johannes-otto/Librecig/Eichhörnchen/doc/img/20181020_093757.jpg

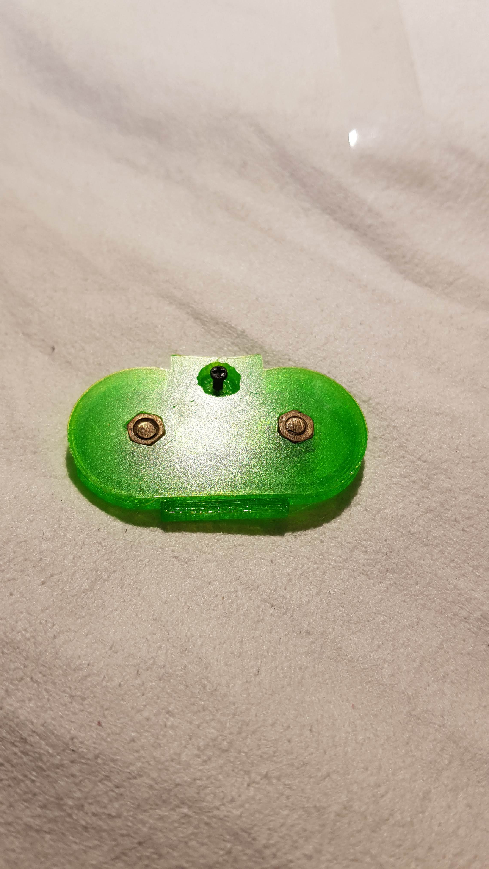
Eichhörnchen/doc/img/20181020_093757.jpg
