johannes-otto/Librecig/Eichhörnchen/doc/img/20181020_103131.jpg

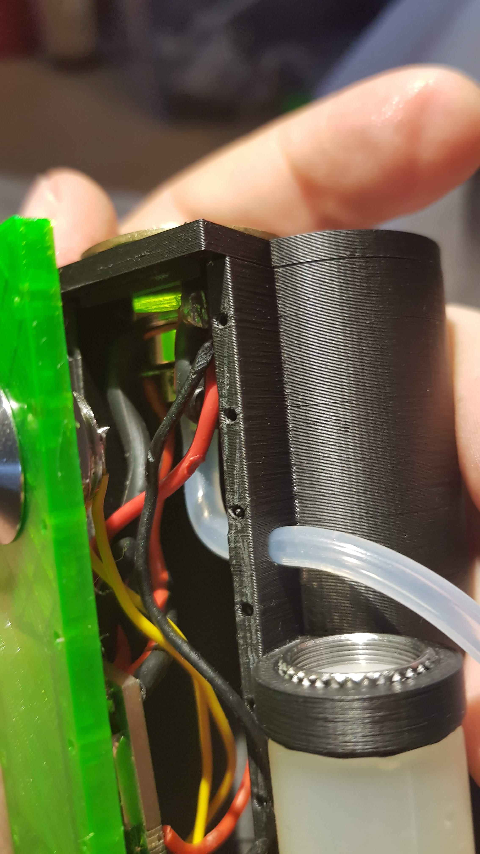
Eichhörnchen/doc/img/20181020_103131.jpg
