johannes-otto/Librecig/Eichhörnchen/doc/img/20181020_105429.jpg

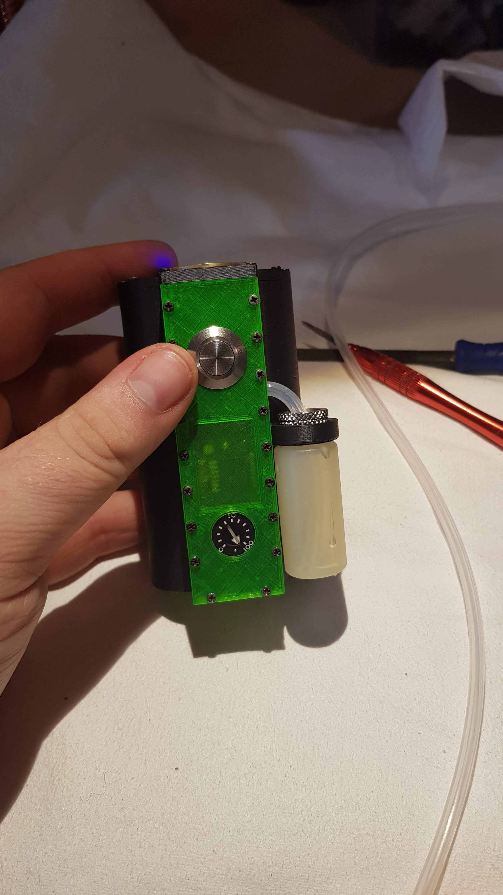
Eichhörnchen/doc/img/20181020_105429.jpg
