johannes-otto/Librecig/Eichhörnchen/doc/img/20181020_105434.jpg

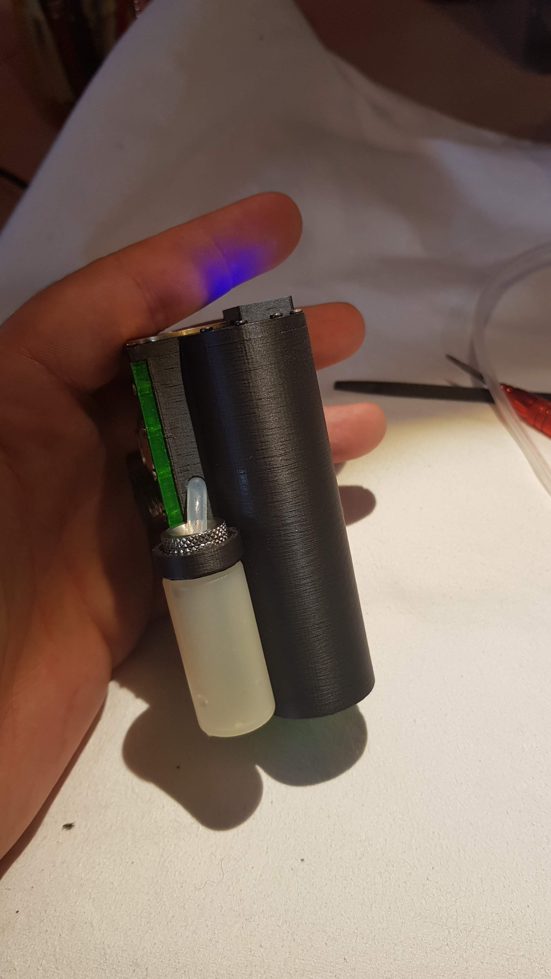
Eichhörnchen/doc/img/20181020_105434.jpg
