johannes-otto/Librecig/Eichhörnchen/doc/img/20181020_105437.jpg

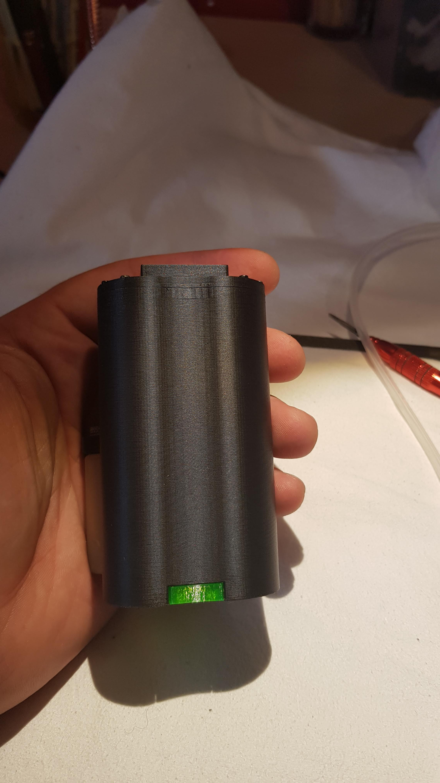
Eichhörnchen/doc/img/20181020_105437.jpg
