johannes-otto/Librecig/Eichhörnchen/doc/img/20181020_105440.jpg

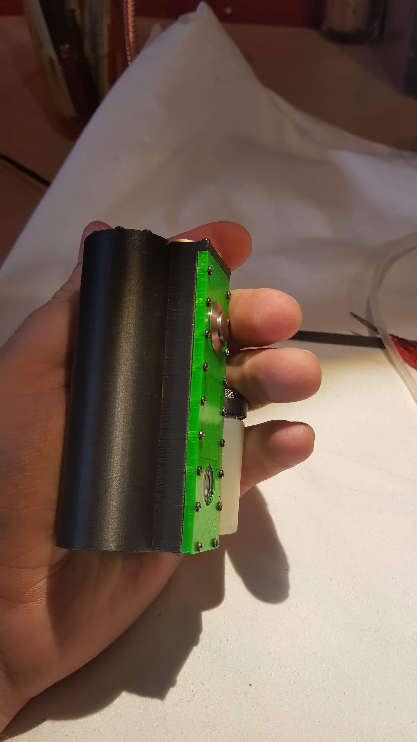
Eichhörnchen/doc/img/20181020_105440.jpg
