johannes-otto/Librecig/Eichhörnchen/doc/img/20181020_105442.jpg

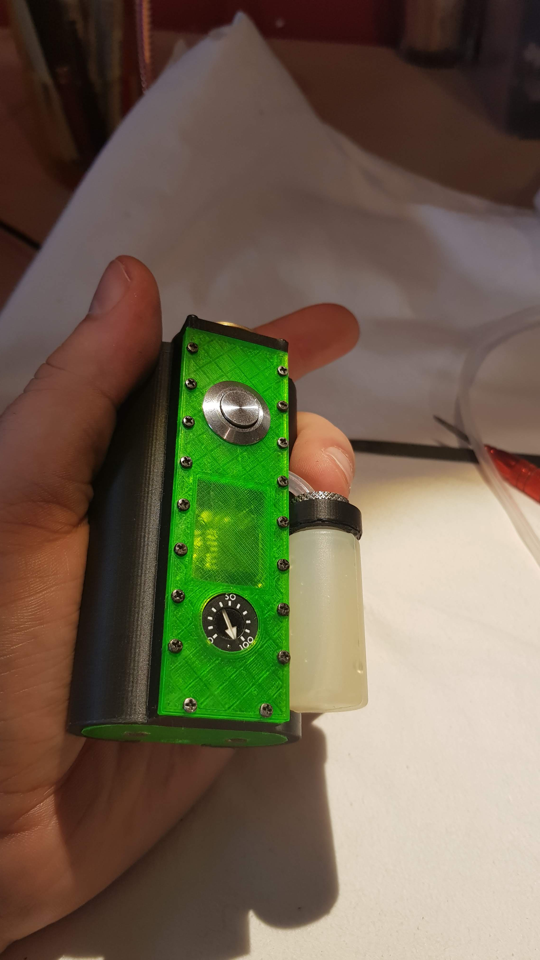
Eichhörnchen/doc/img/20181020_105442.jpg
