johannes-otto/Librecig/Eichhörnchen/doc/img/20181020_105443.jpg

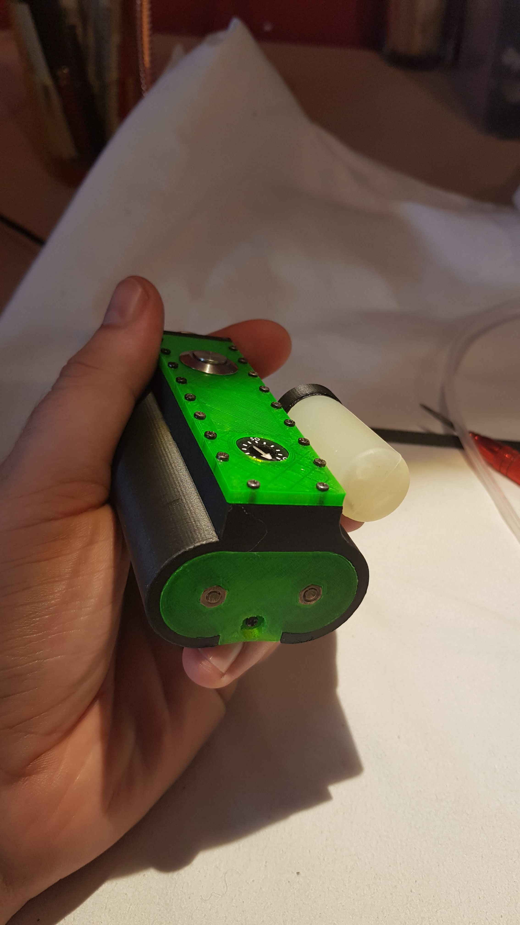
Eichhörnchen/doc/img/20181020_105443.jpg
