johannes-otto/Librecig/Eichhörnchen/doc/img/20181020_105446.jpg

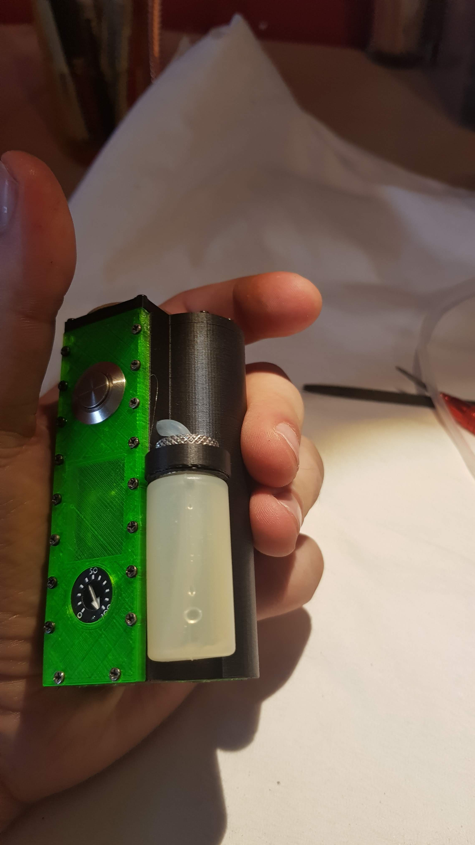
Eichhörnchen/doc/img/20181020_105446.jpg
