johannes-otto/Librecig/Ratte and Variations/doc/images/wire diagrams/ANT PWM Wring Diagram.jpg

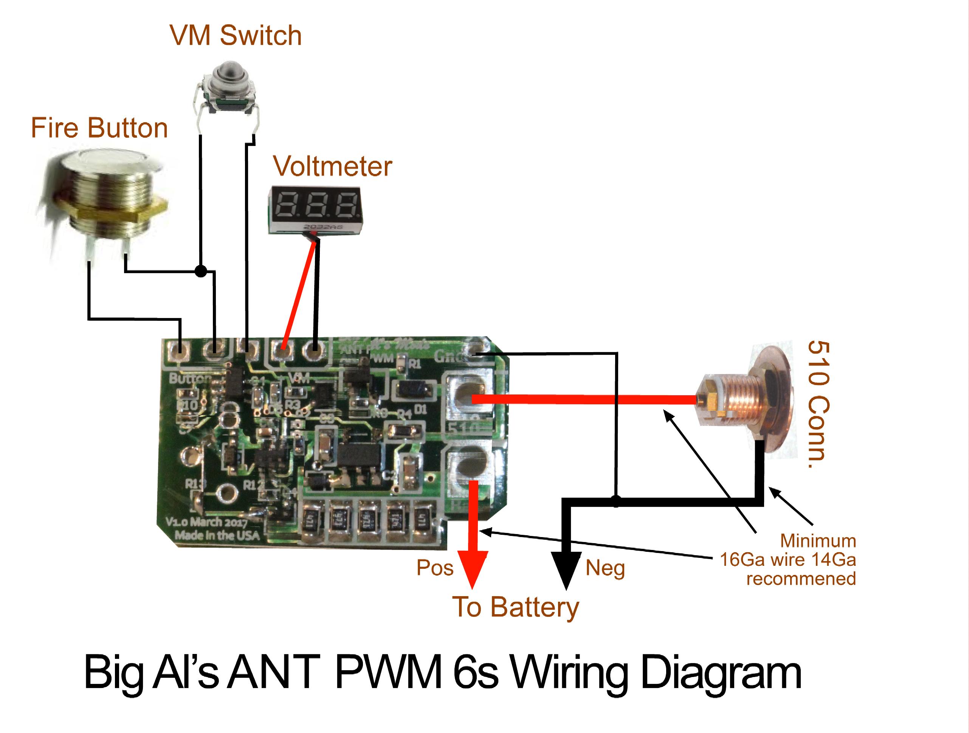
Ratte and Variations/doc/images/wire diagrams/ANT PWM Wring Diagram.jpg
