johannes-otto/Librecig/Großwiesel/Großwiesel v7_Großwiesel v7_body_Großwiesel v7.stl

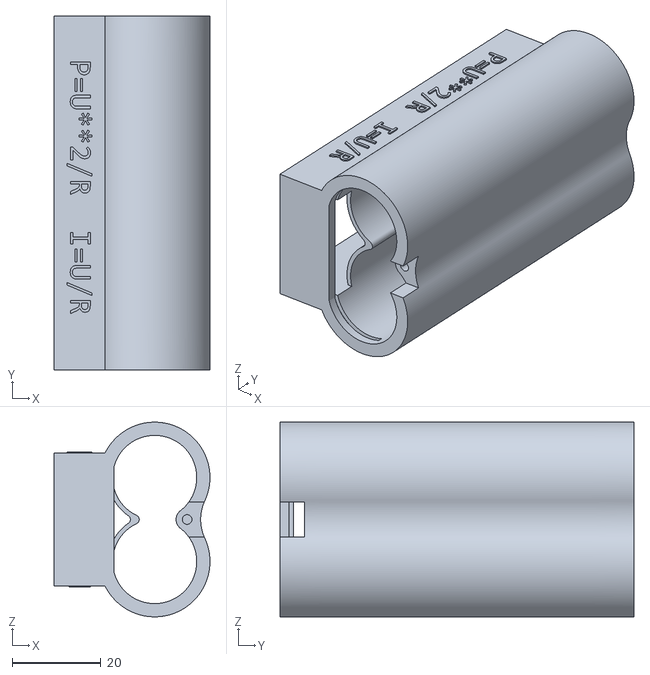
[picture p41: CAD file, 2018-12-22]
Großwiesel/Großwiesel v7_Großwiesel v7_body_Großwiesel v7.stl
35.2 x 80.0 x 44.0
