johannes-otto/Librecig/Großwiesel/v7/Großwiesel v7_Großwiesel v7_top_Großwiesel v7.stl

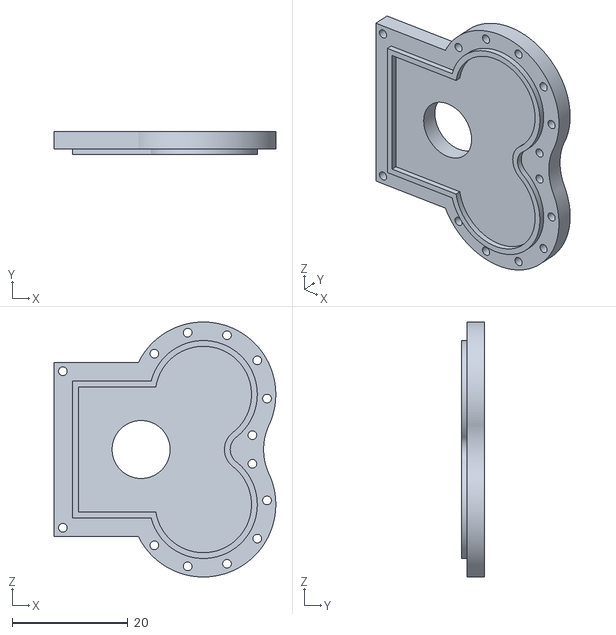
[picture p42: CAD file, 2018-12-22]
Großwiesel/v7/Großwiesel v7_Großwiesel v7_top_Großwiesel v7.stl
38.2 x 4.00 x 44.0
