johannes-otto/Librecig/Ratte and Variations/Leviatan/Leviathan Body.stl

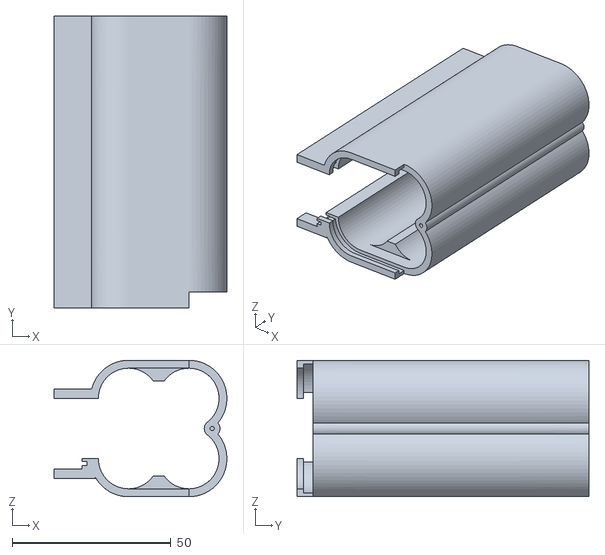
[picture p43: CAD file, 2018-06-19]
Ratte and Variations/Leviatan/Leviathan Body.stl
54.4 x 92.0 x 43.0
