johannes-otto/Librecig/Ratte and Variations/Ratte/Ratte Top.stl

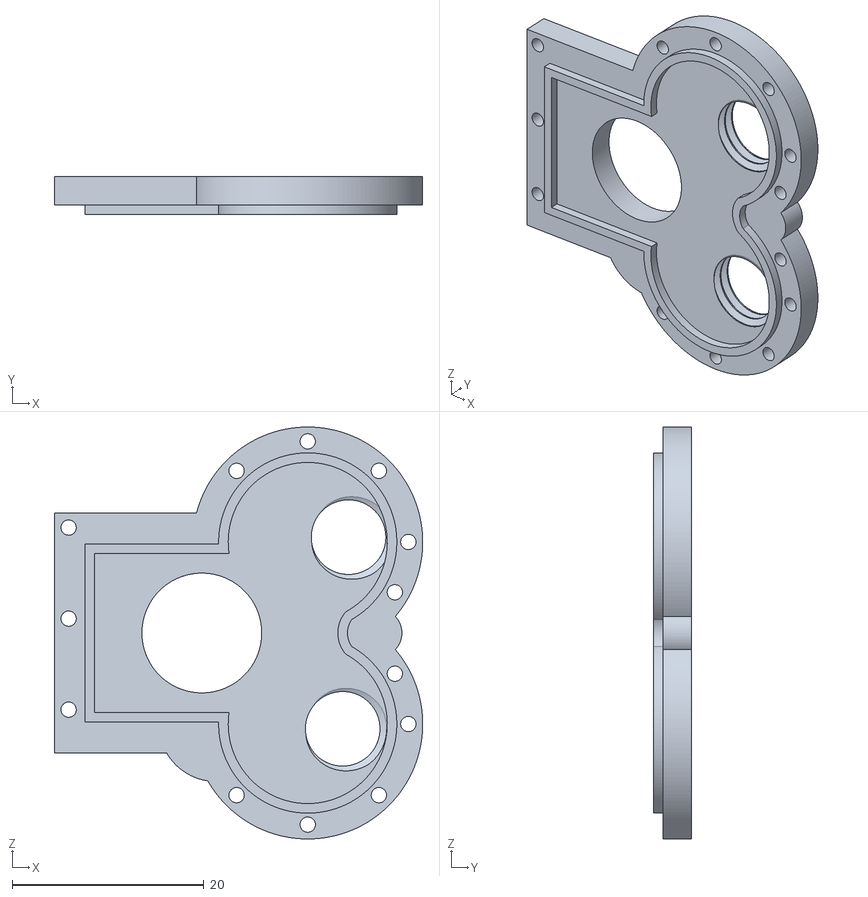
[picture p44: CAD file, 2018-10-05]
Ratte and Variations/Ratte/Ratte Top.stl
38.5 x 4.00 x 43.0
