johannes-otto/Librecig/Ratte and Variations/Wisent/Wisent Battery Door.stl

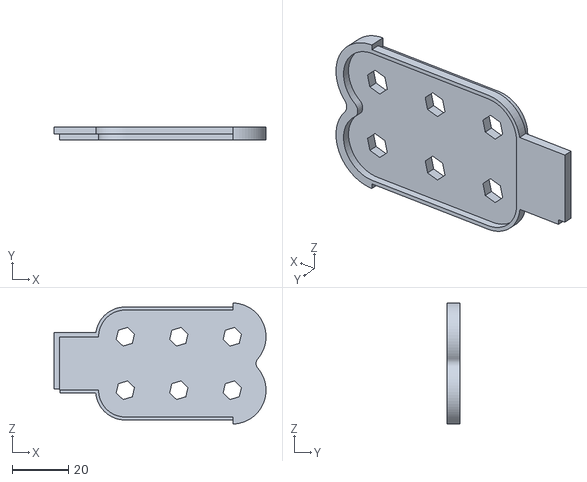
[picture p46: CAD file, 2018-06-10]
Ratte and Variations/Wisent/Wisent Battery Door.stl
75.3 x 4.70 x 43.0
