johannes-otto/Librecig/Wiesel/v4/Wiesel2 v4_Wiesel2 v4_battery door new_Wiesel2 v4.stl

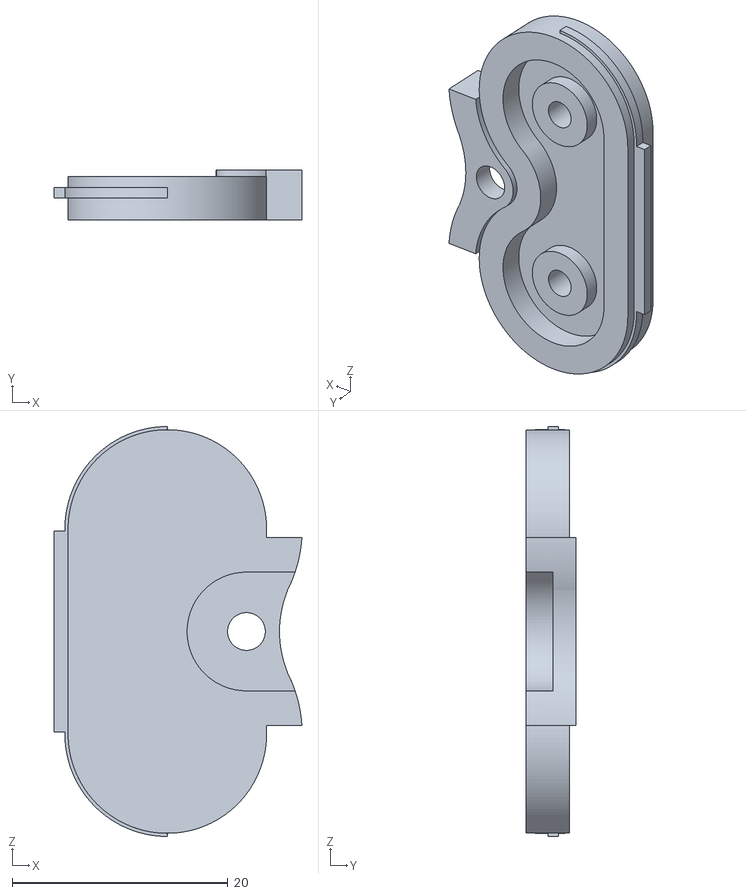
[picture p47: CAD file, 2018-12-22]
Wiesel/v4/Wiesel2 v4_Wiesel2 v4_battery door new_Wiesel2 v4.stl
23.0 x 4.60 x 38.0
