johannes-otto/Librecig/Wiesel/Wiesel 1/v10/spanner.stl

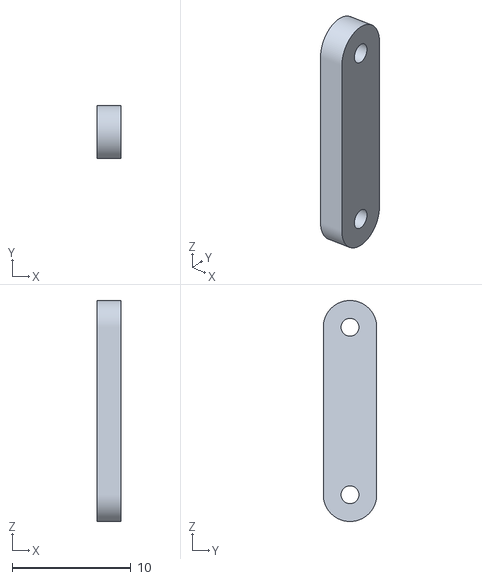
[picture p48: CAD file, 2018-12-09]
Wiesel/Wiesel 1/v10/spanner.stl
2.00 x 4.50 x 18.6
