johannes-otto/Librecig/Battery Compartments/Jonny Drips Subohm Survival Kit/Subohm Survival Kit v4_Subohm Survival Kit v4_Insert_Subohm Survival Kit v4.stl

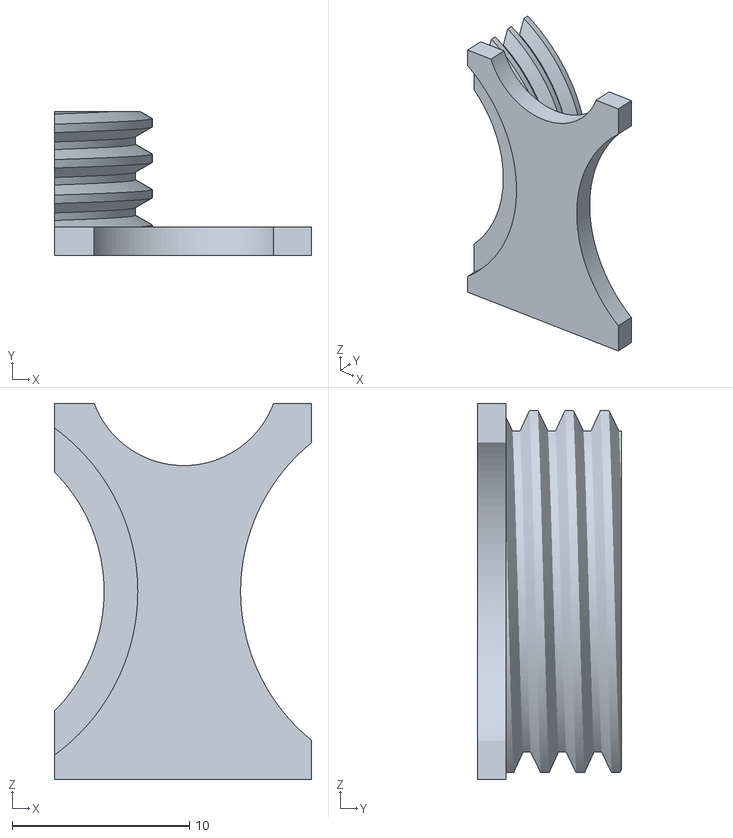
[picture p49: CAD file, 2018-12-22]
Battery Compartments/Jonny Drips Subohm Survival Kit/Subohm Survival Kit v4_Subohm Survival Kit v4_Insert_Subohm Survival Kit v4.stl
14.5 x 8.10 x 21.2
