johannes-otto/Librecig/Eichhörnchen/V1/beautylip.stl

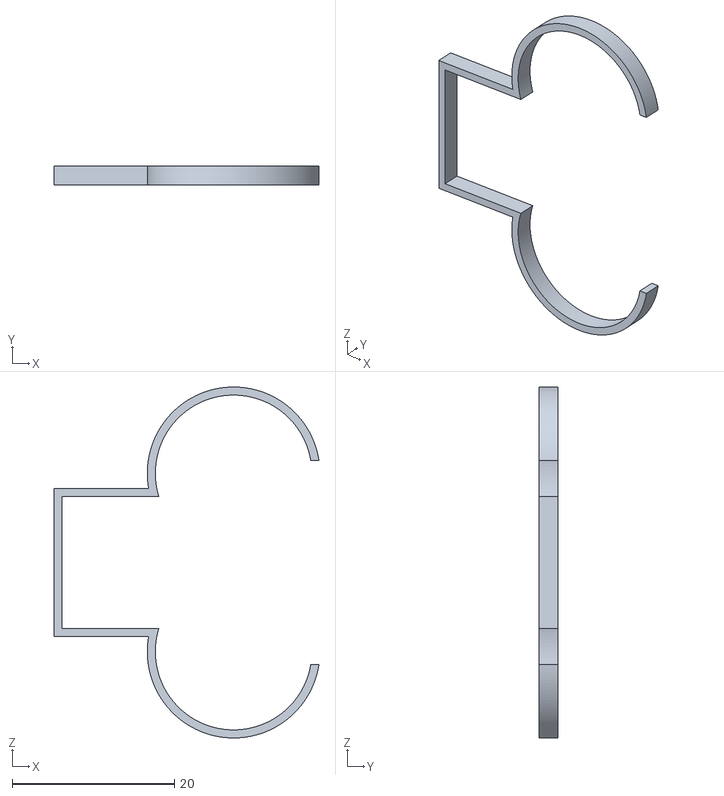
[picture p50: CAD file, 2018-10-05]
Eichhörnchen/V1/beautylip.stl
32.7 x 2.40 x 43.3
