johannes-otto/Librecig/Eichhörnchen/V2 No Squonk/body.stl

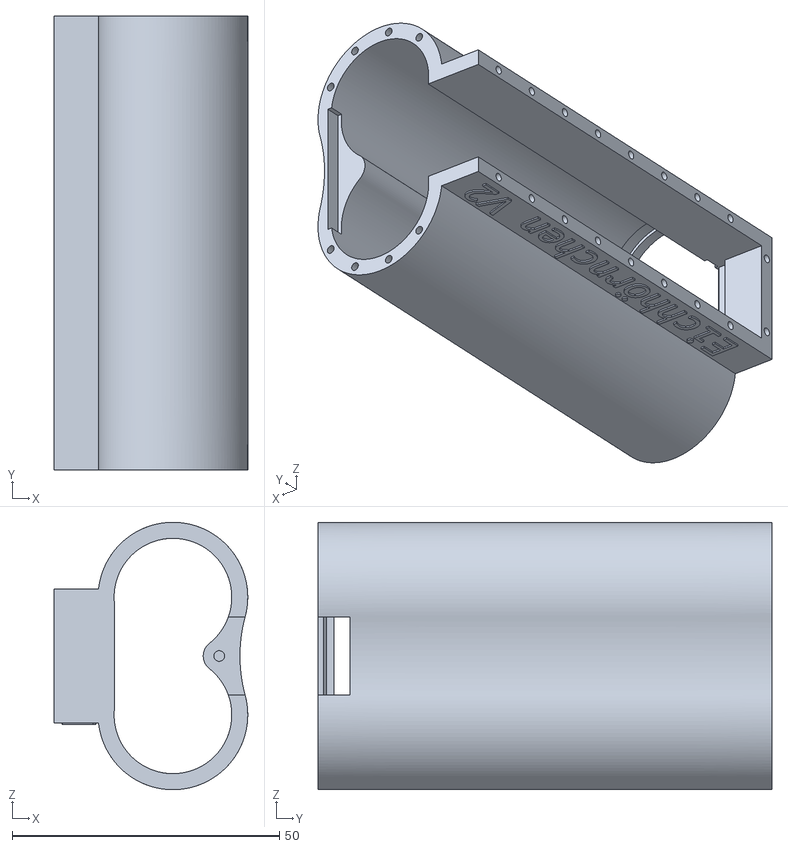
[picture p51: CAD file, 2018-11-24]
Eichhörnchen/V2 No Squonk/body.stl
36.2 x 84.9 x 50.0
