johannes-otto/Librecig/Ratte and Variations/Leviatan/Leviathan Battery Cover.stl

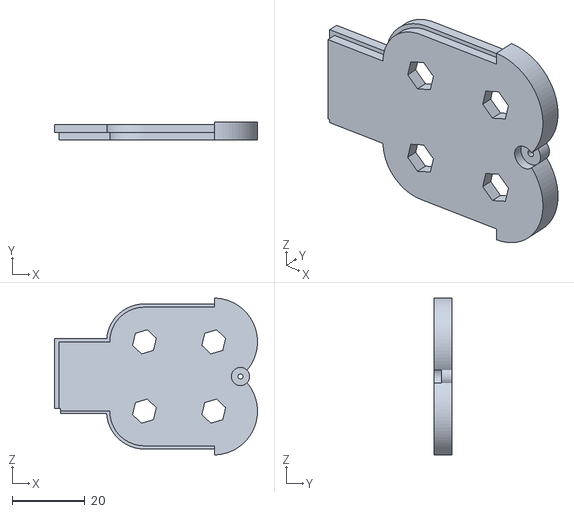
[picture p52: CAD file, 2018-06-19]
Ratte and Variations/Leviatan/Leviathan Battery Cover.stl
55.6 x 4.90 x 43.0
