johannes-otto/Librecig/Ratte and Variations/Ratte/Ratte Body.stl

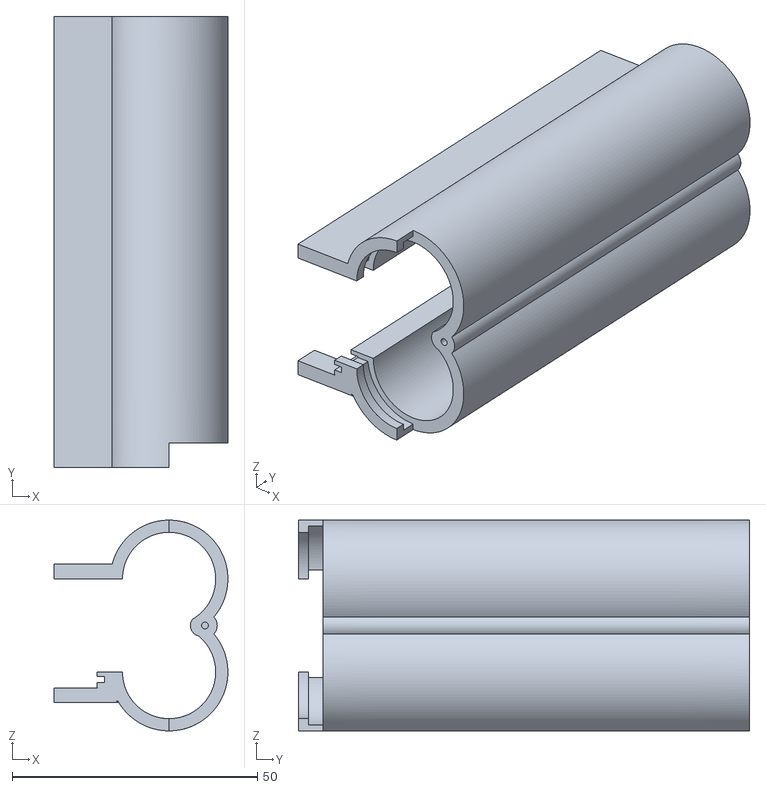
[picture p53: CAD file, 2018-10-05]
Ratte and Variations/Ratte/Ratte Body.stl
35.5 x 92.0 x 43.0
