johannes-otto/Librecig/Ratte and Variations/shared parts/iPWM_Front.stl

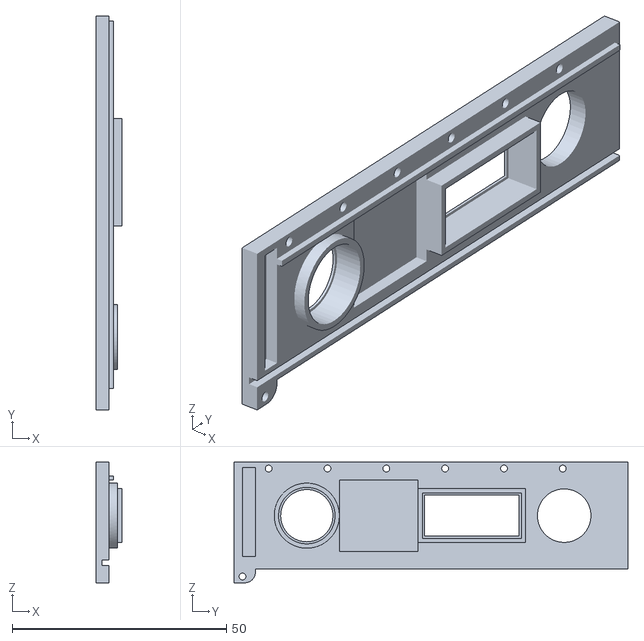
[picture p54: CAD file, 2018-10-05]
Ratte and Variations/shared parts/iPWM_Front.stl
6.00 x 92.0 x 28.2
