johannes-otto/Librecig/Ratte and Variations/Wisent/Wisent Top.stl

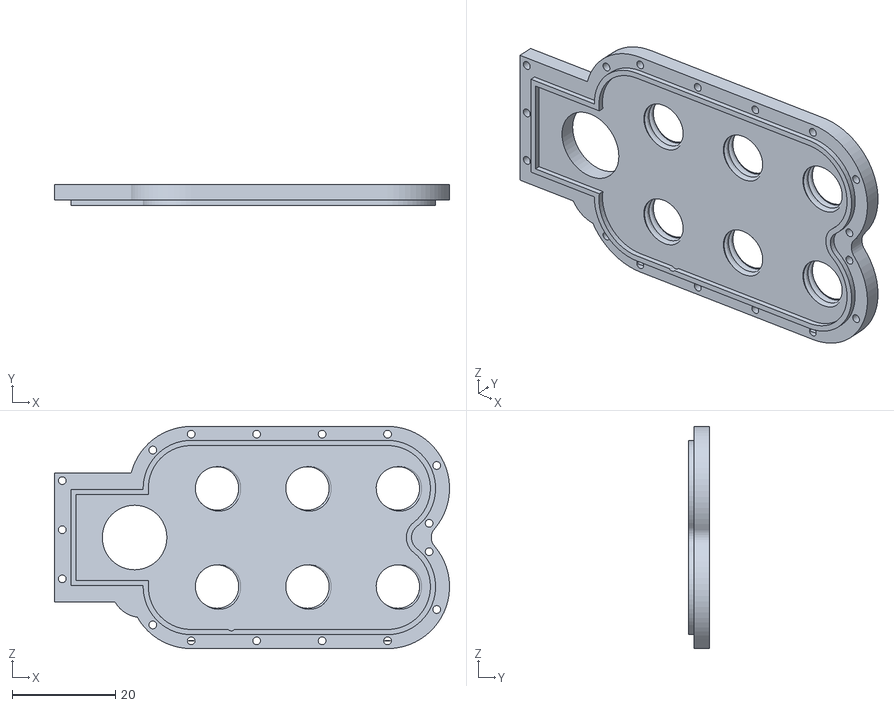
[picture p55: CAD file, 2018-06-10]
Ratte and Variations/Wisent/Wisent Top.stl
76.4 x 4.00 x 43.0
