johannes-otto/Librecig/Wiesel/Wiesel 1/v10/battery door.stl

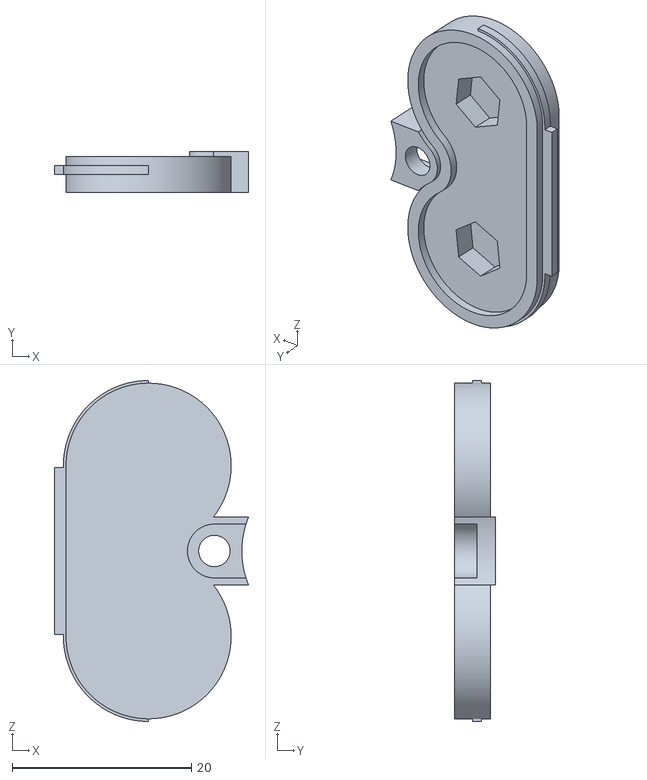
[picture p56: CAD file, 2018-12-09]
Wiesel/Wiesel 1/v10/battery door.stl
21.6 x 4.60 x 38.0
