johannes-otto/Librecig/Eichhörnchen/V2 No Squonk/top.stl

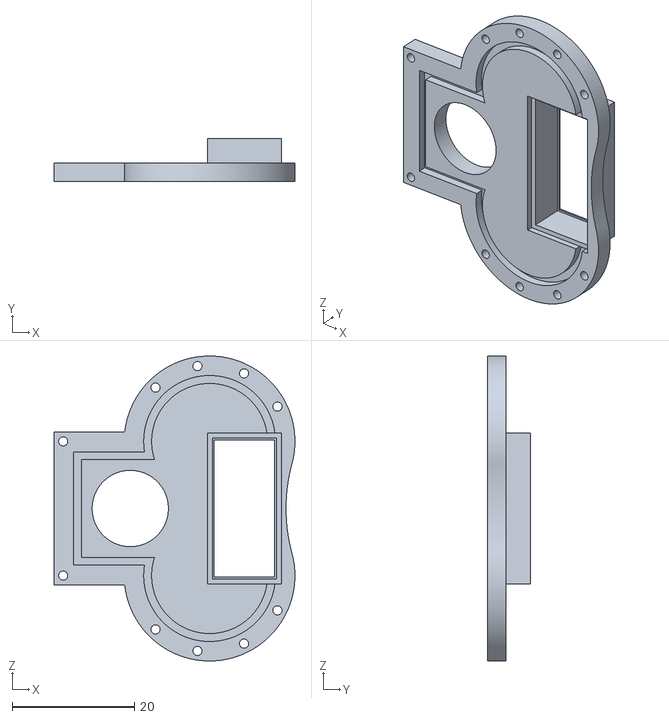
[picture p57: CAD file, 2018-11-24]
Eichhörnchen/V2 No Squonk/top.stl
39.5 x 7.00 x 50.0
