johannes-otto/Librecig/Ratte and Variations/Leviatan/Leviathan Top Pole Spring.stl

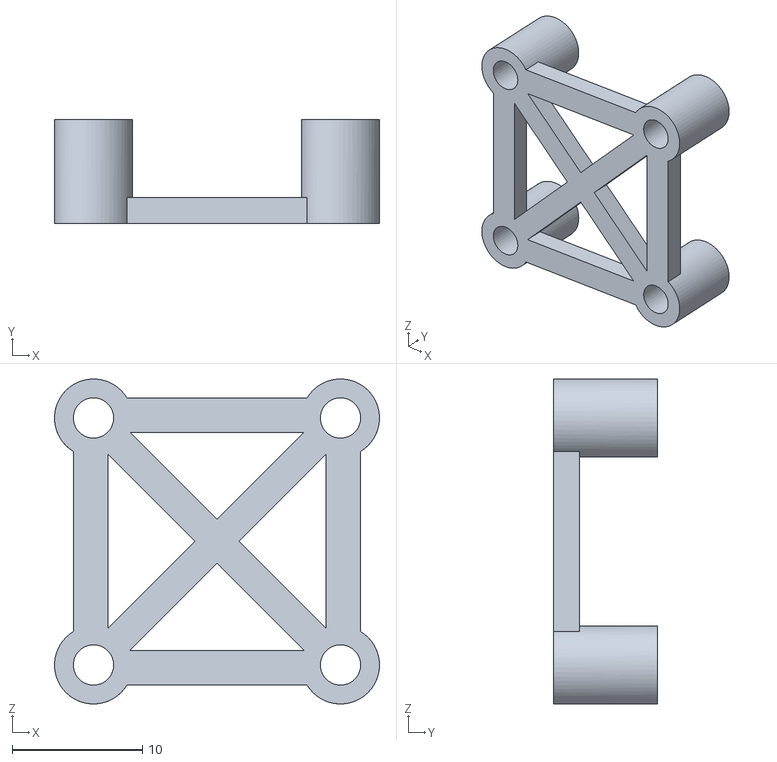
[picture p58: CAD file, 2018-06-19]
Ratte and Variations/Leviatan/Leviathan Top Pole Spring.stl
25.0 x 8.00 x 25.0
