johannes-otto/Librecig/Ratte and Variations/Ratte/Ratte Battery Cover.stl

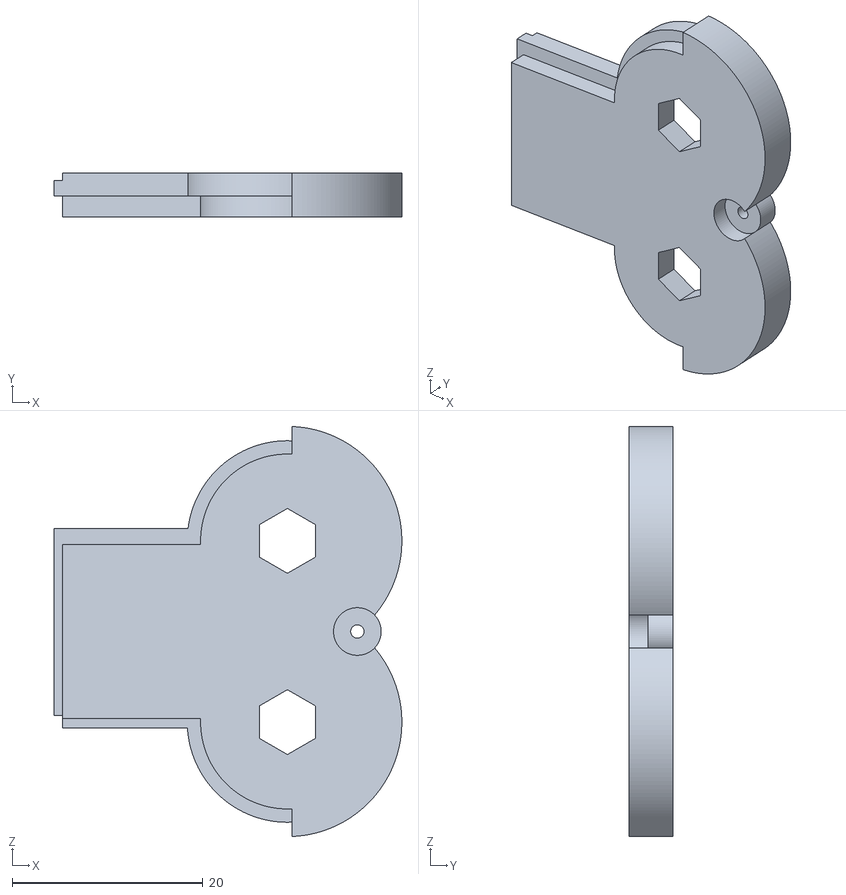
[picture p59: CAD file, 2018-10-05]
Ratte and Variations/Ratte/Ratte Battery Cover.stl
36.5 x 4.60 x 43.0
