johannes-otto/Librecig/Ratte and Variations/shared parts/Mosfet_Front.stl

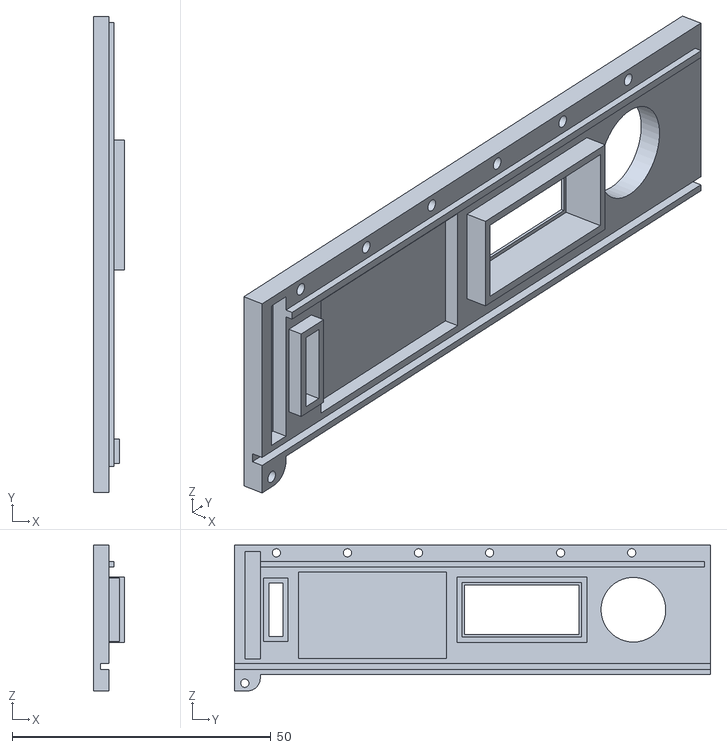
[picture p60: CAD file, 2018-10-05]
Ratte and Variations/shared parts/Mosfet_Front.stl
6.00 x 92.0 x 28.2
