johannes-otto/Librecig/Ratte and Variations/Wisent/Wisent Top Pole Cover 2.stl

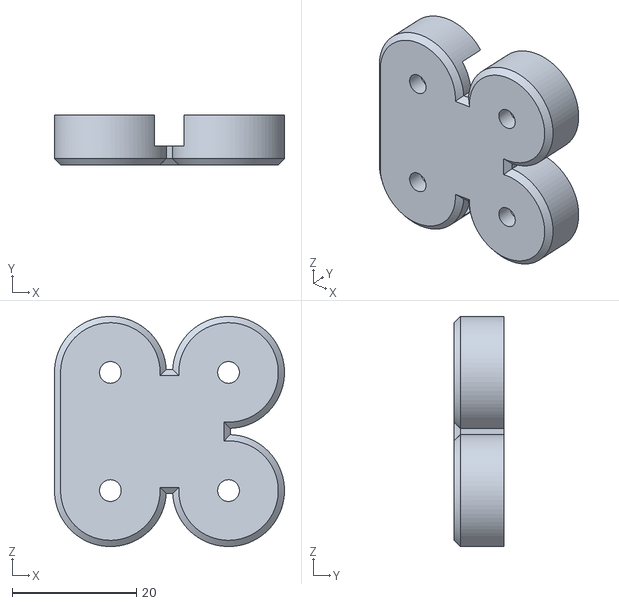
[picture p61: CAD file, 2018-06-03]
Ratte and Variations/Wisent/Wisent Top Pole Cover 2.stl
37.0 x 8.00 x 37.0
