johannes-otto/Librecig/Wiesel/v4/Wiesel2 v4_Wiesel2 v4_terminal_Wiesel2 v4.stl

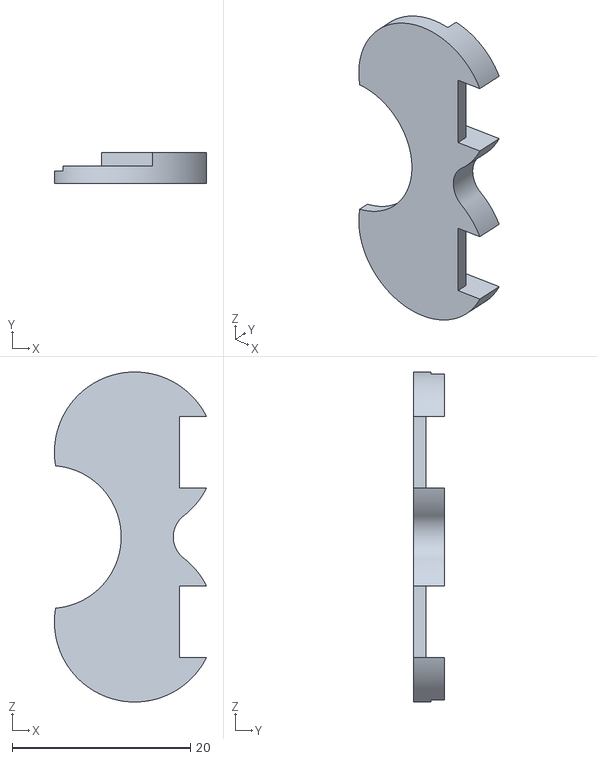
[picture p62: CAD file, 2018-12-22]
Wiesel/v4/Wiesel2 v4_Wiesel2 v4_terminal_Wiesel2 v4.stl
17.1 x 3.50 x 37.0
