johannes-otto/Librecig/Wiesel/Wiesel 1/v10/25mm adapter.stl

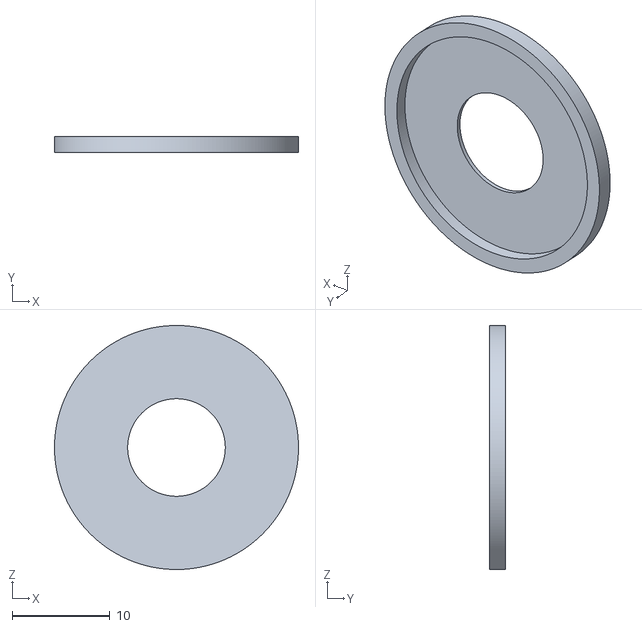
[picture p63: CAD file, 2018-12-09]
Wiesel/Wiesel 1/v10/25mm adapter.stl
25.0 x 1.60 x 25.0
