johannes-otto/Librecig/Eichhörnchen/V2 No Squonk/terminal.stl

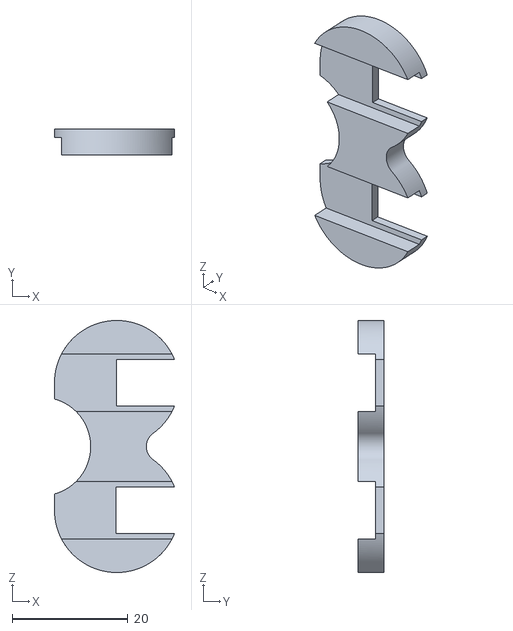
[picture p64: CAD file, 2018-11-24]
Eichhörnchen/V2 No Squonk/terminal.stl
20.7 x 4.50 x 43.5
