johannes-otto/Librecig/Großwiesel/Großwiesel v7_Großwiesel v7_cable clip long_Großwiesel v7.stl

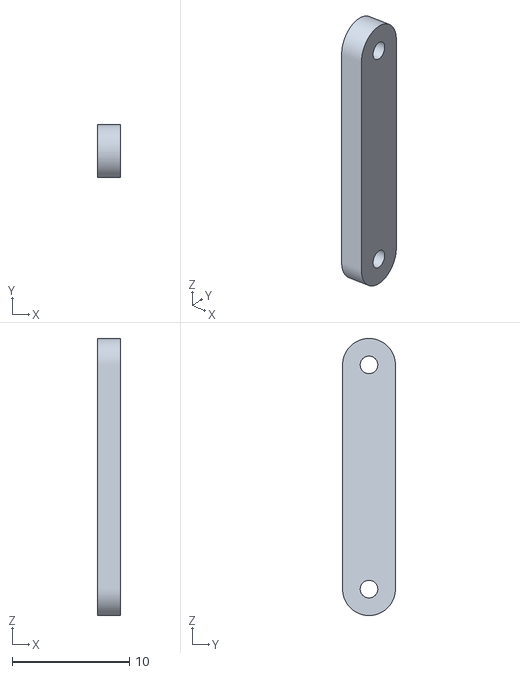
[picture p65: CAD file, 2018-12-22]
Großwiesel/Großwiesel v7_Großwiesel v7_cable clip long_Großwiesel v7.stl
2.00 x 4.50 x 23.6
