johannes-otto/Librecig/Ratte and Variations/Leviatan/Leviathan Top.stl

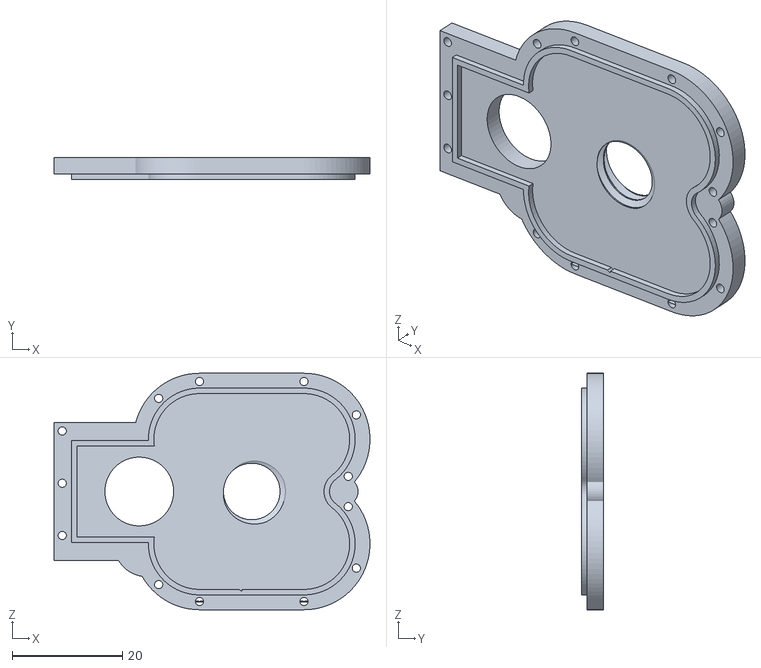
[picture p66: CAD file, 2018-06-19]
Ratte and Variations/Leviatan/Leviathan Top.stl
57.4 x 4.00 x 43.0
