johannes-otto/Librecig/Ratte and Variations/shared parts/New Squonk Side Panel 2.stl

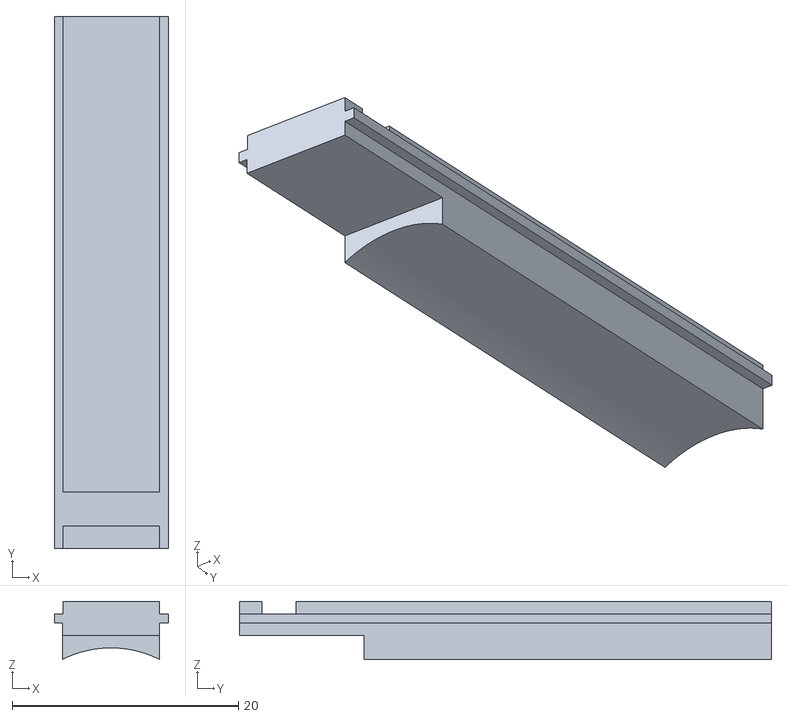
[picture p67: CAD file, 2018-10-05]
Ratte and Variations/shared parts/New Squonk Side Panel 2.stl
10.1 x 47.0 x 5.13
