johannes-otto/Librecig/Ratte and Variations/Wisent/Wisent Top Pole Cover 1.stl

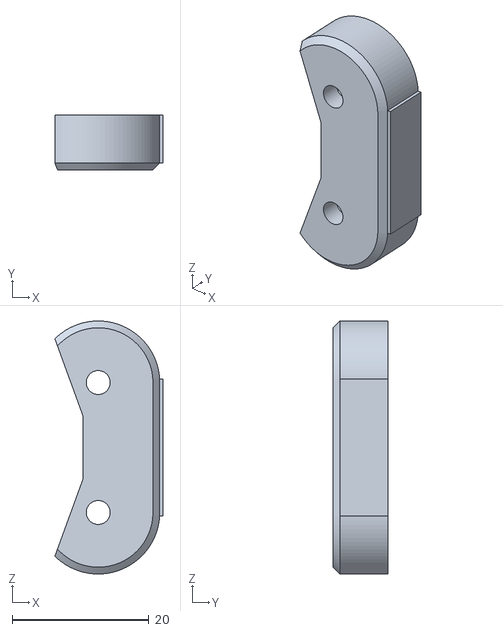
[picture p68: CAD file, 2018-06-02]
Ratte and Variations/Wisent/Wisent Top Pole Cover 1.stl
15.8 x 8.00 x 37.0
