johannes-otto/Librecig/Wiesel/Wiesel 1/v10/terminal.stl

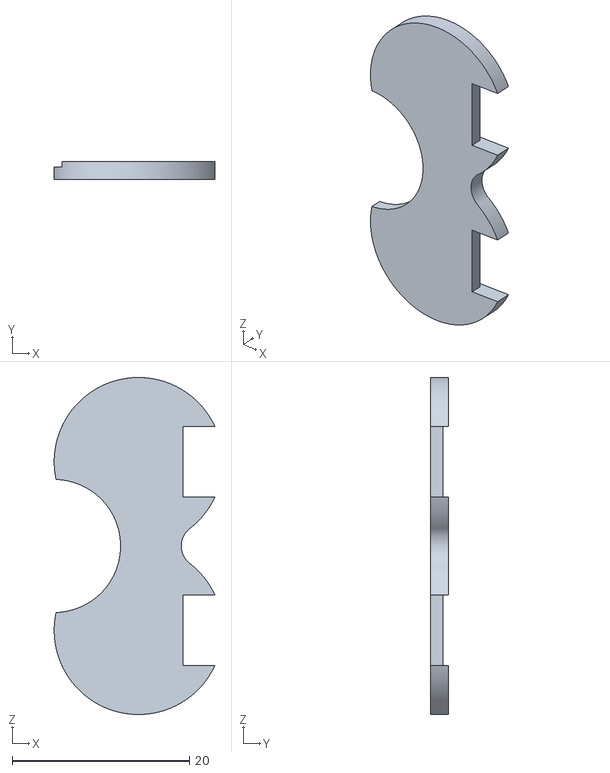
[picture p69: CAD file, 2018-12-09]
Wiesel/Wiesel 1/v10/terminal.stl
18.1 x 2.00 x 38.0
