johannes-otto/Librecig/Eichhörnchen/V2 No Squonk/front mosfet.stl

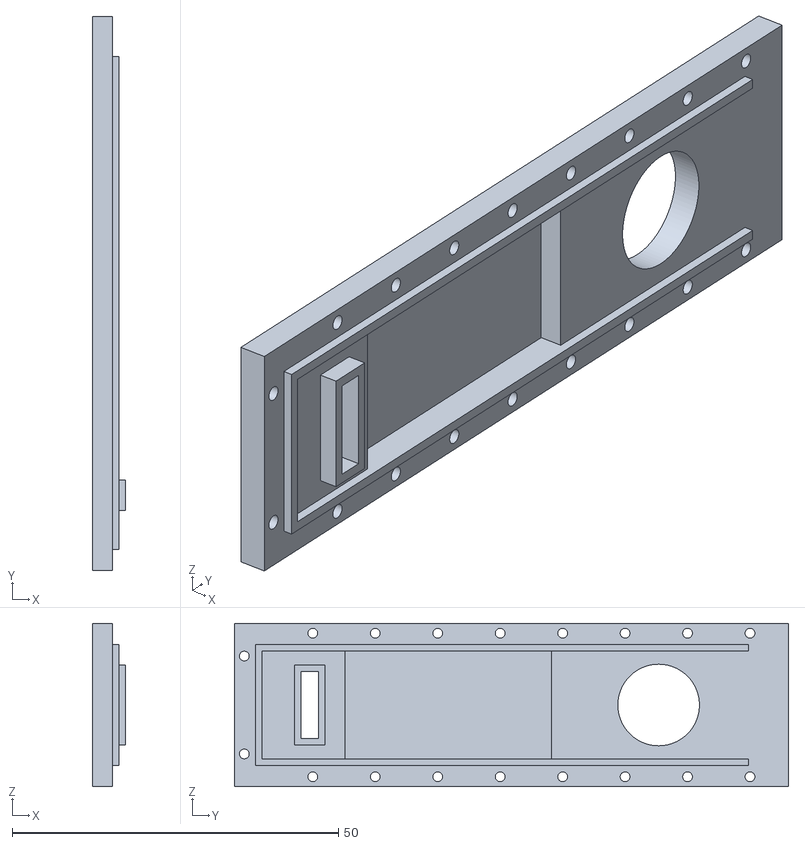
[picture p70: CAD file, 2018-11-24]
Eichhörnchen/V2 No Squonk/front mosfet.stl
5.00 x 84.9 x 25.0
