johannes-otto/Librecig/Großwiesel/v7/Großwiesel v7_Großwiesel v7_front_Großwiesel v7.stl

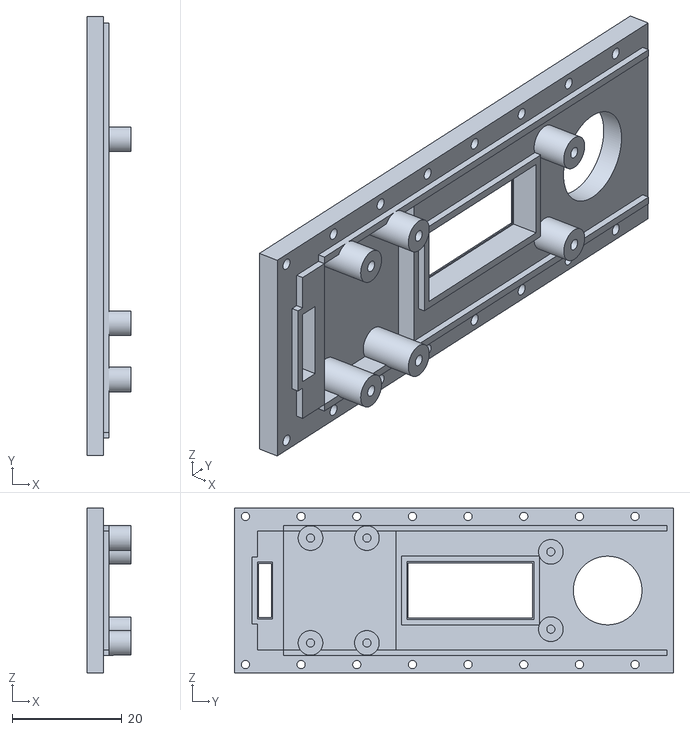
[picture p71: CAD file, 2018-12-22]
Großwiesel/v7/Großwiesel v7_Großwiesel v7_front_Großwiesel v7.stl
8.00 x 80.0 x 30.0
