johannes-otto/Librecig/Wiesel/v4/Wiesel2 v4_Wiesel2 v4_top_Wiesel2 v4.stl

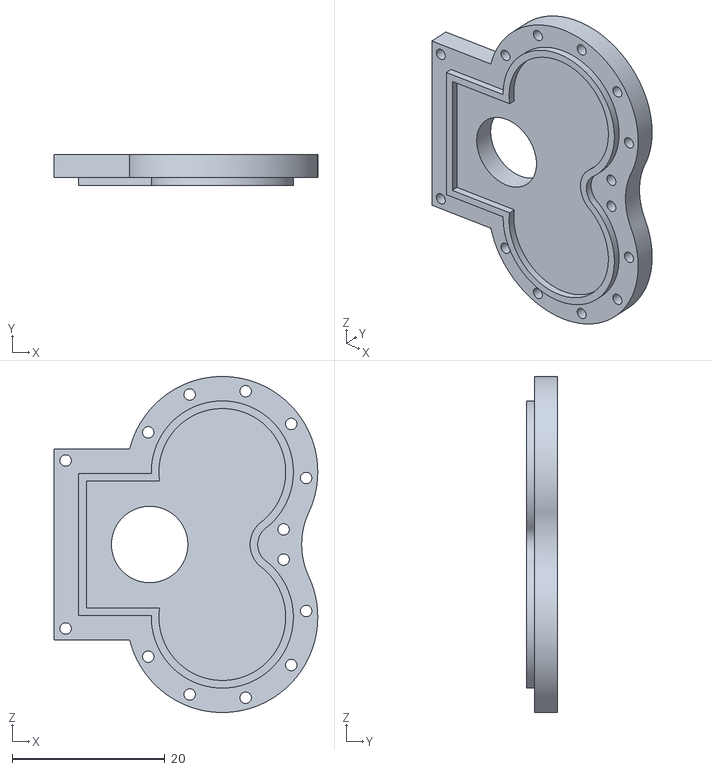
[picture p72: CAD file, 2018-12-22]
Wiesel/v4/Wiesel2 v4_Wiesel2 v4_top_Wiesel2 v4.stl
34.5 x 4.00 x 44.0
