johannes-otto/Librecig/Eichhörnchen/V2 No Squonk/battery door.stl

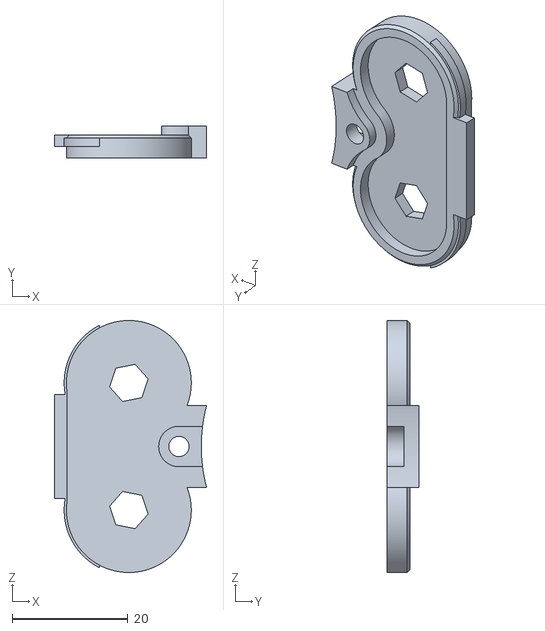
[picture p73: CAD file, 2018-11-24]
Eichhörnchen/V2 No Squonk/battery door.stl
26.4 x 5.60 x 43.6
