johannes-otto/Librecig/Wiesel/Wiesel 1/v10/body.stl

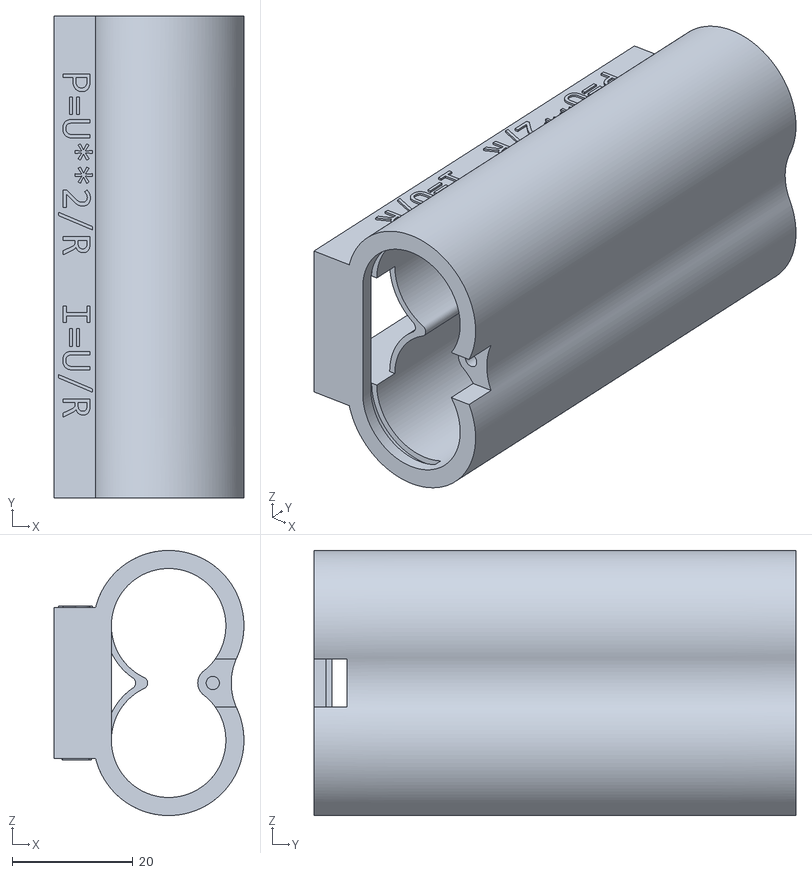
[picture p74: CAD file, 2018-12-09]
Wiesel/Wiesel 1/v10/body.stl
31.5 x 80.0 x 44.0
