johannes-otto/Librecig/Ratte and Variations/shared parts/Plain Side Panel.stl

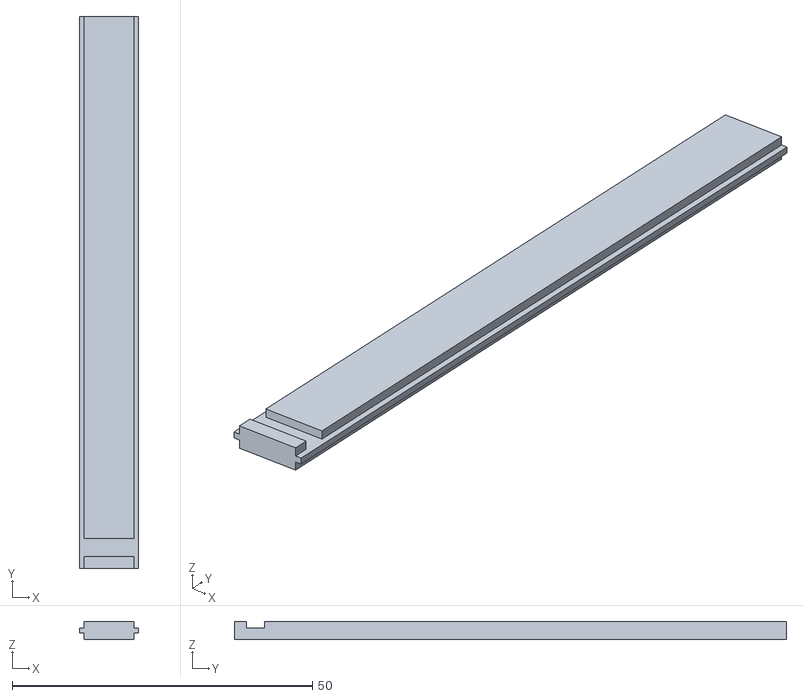
[picture p75: CAD file, 2018-06-02]
Ratte and Variations/shared parts/Plain Side Panel.stl
9.91 x 92.0 x 3.00
