johannes-otto/Librecig/Ratte and Variations/shared parts/Squonk Side Panel 2.stl

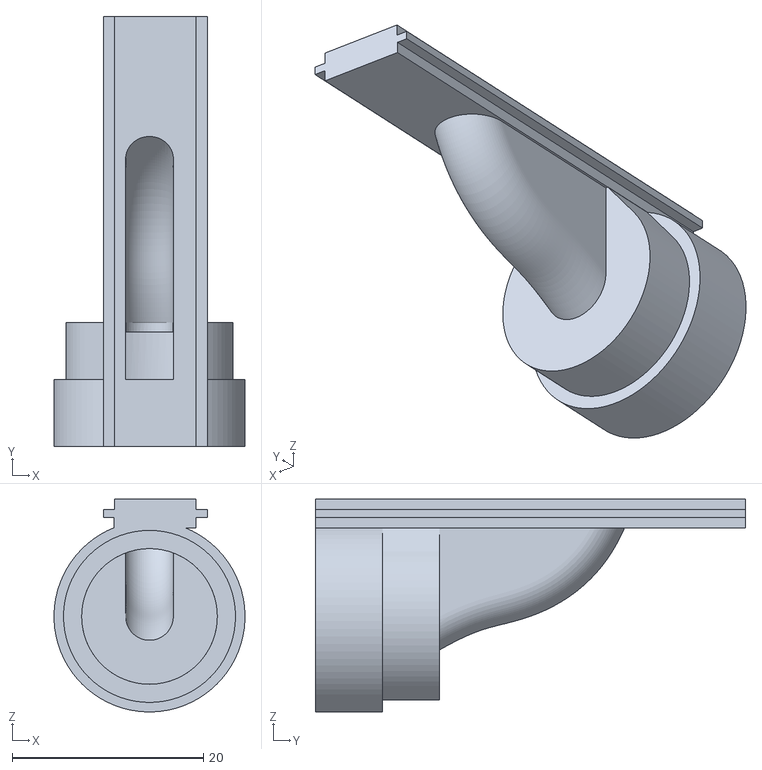
[picture p76: CAD file, 2018-06-02]
Ratte and Variations/shared parts/Squonk Side Panel 2.stl
20.0 x 45.0 x 22.3
