johannes-otto/Librecig/Ratte and Variations/shared parts/Squonk Side Panel 1.stl

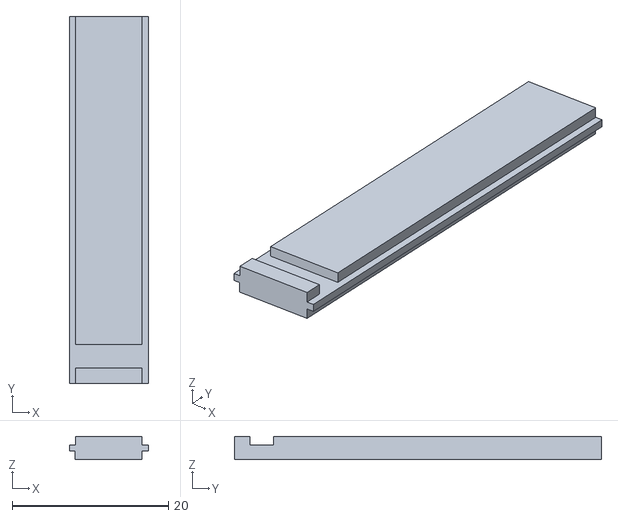
[picture p77: CAD file, 2018-06-02]
Ratte and Variations/shared parts/Squonk Side Panel 1.stl
10.1 x 47.0 x 3.00
