johannes-otto/Librecig/Ratte and Variations/doc/images/building/wisent/done.png

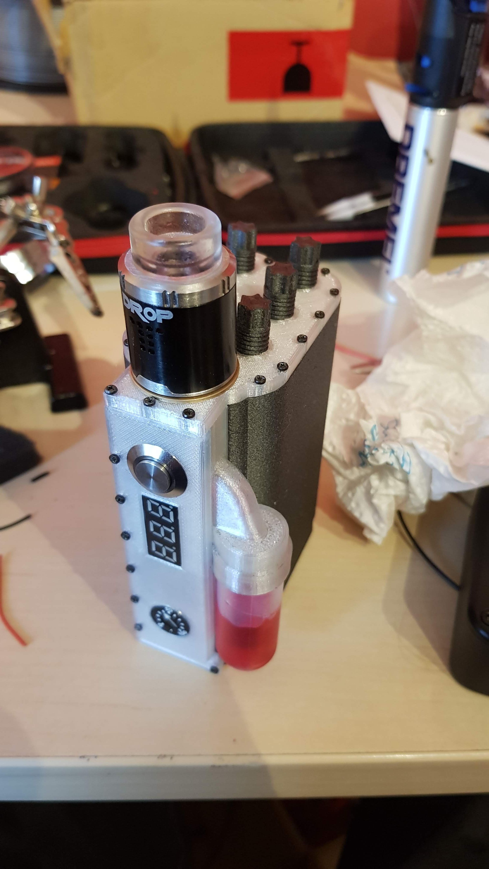
Ratte and Variations/doc/images/building/wisent/done.png
