johannes-otto/Librecig/Ratte and Variations/doc/images/building/wisent/front_plate_insert_vm.png

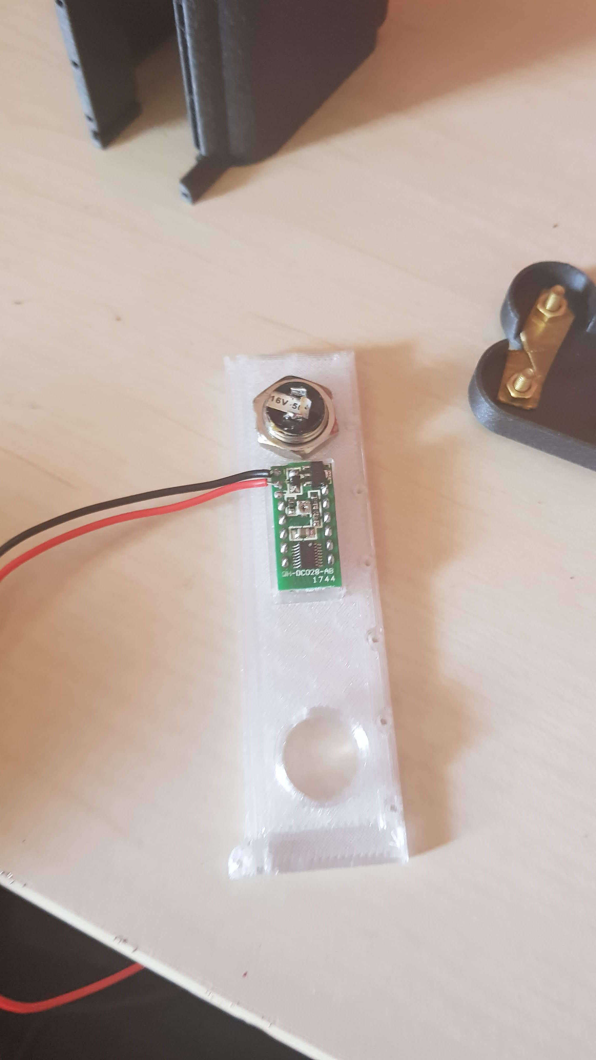
Ratte and Variations/doc/images/building/wisent/front_plate_insert_vm.png
