johannes-otto/Librecig/Ratte and Variations/doc/images/building/wisent/front_plate_vm+sw.png

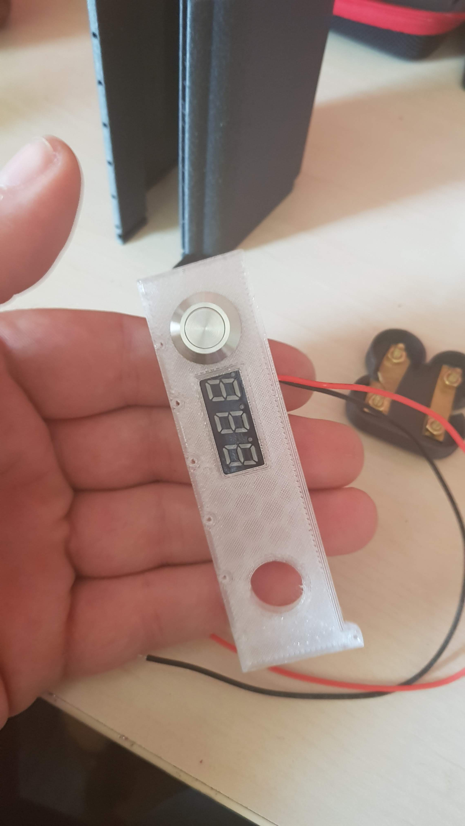
Ratte and Variations/doc/images/building/wisent/front_plate_vm+sw.png
