johannes-otto/Librecig/Ratte and Variations/doc/images/building/wisent/ipwm.png

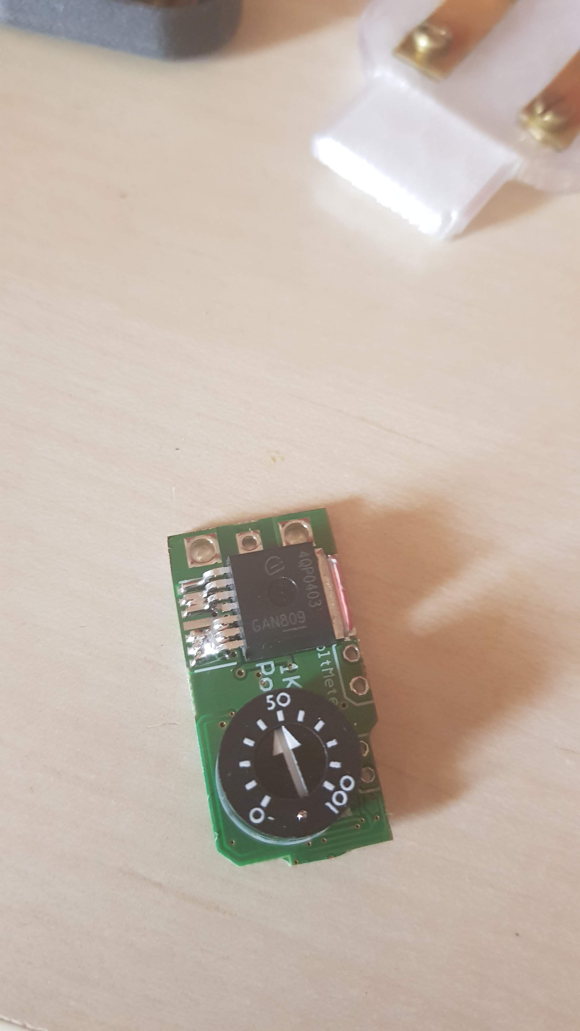
Ratte and Variations/doc/images/building/wisent/ipwm.png
