johannes-otto/Librecig/Ratte and Variations/doc/images/building/wisent/new_front_plate_with_vm.png

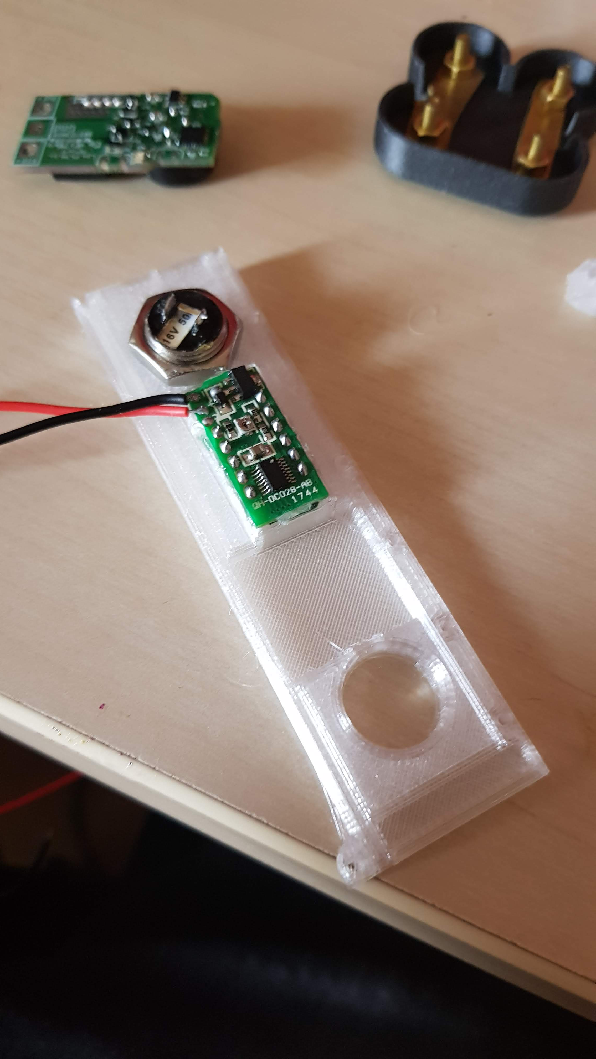
Ratte and Variations/doc/images/building/wisent/new_front_plate_with_vm.png
