johannes-otto/Librecig/Ratte and Variations/doc/images/building/wisent/preparing_screw_holes.png

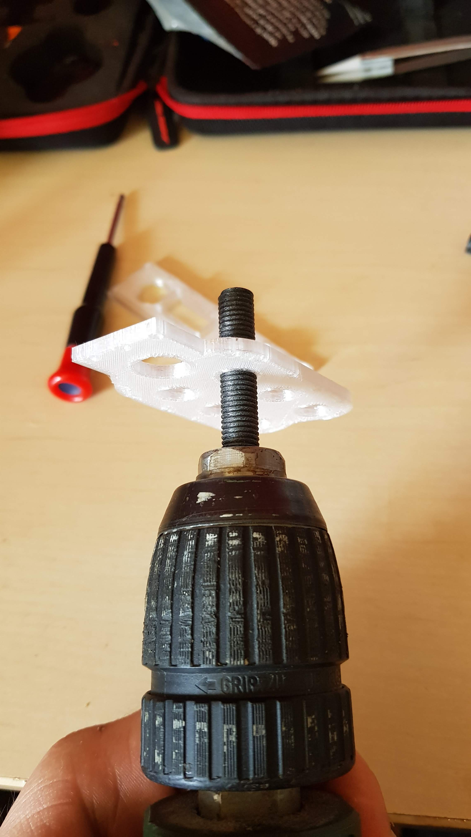
Ratte and Variations/doc/images/building/wisent/preparing_screw_holes.png
