johannes-otto/Librecig/Ratte and Variations/doc/images/building/wisent/preparing_squonk_bottle5.png

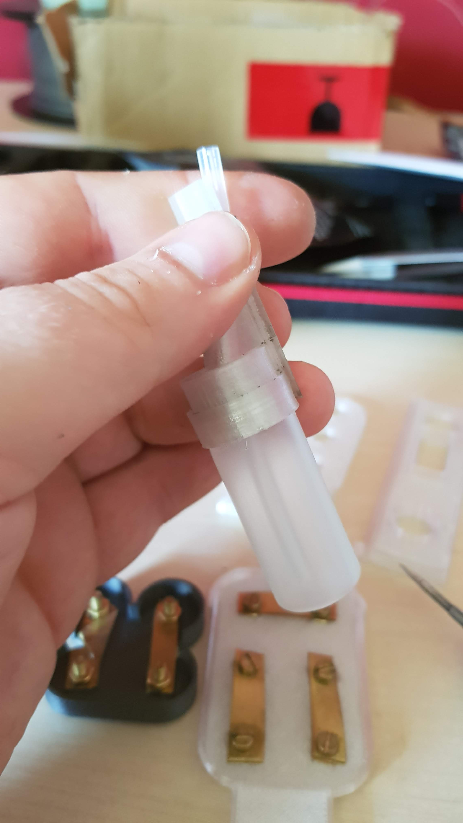
Ratte and Variations/doc/images/building/wisent/preparing_squonk_bottle5.png
