johannes-otto/Librecig/Ratte and Variations/doc/images/building/wisent/preparing_squonk_bottle17.png

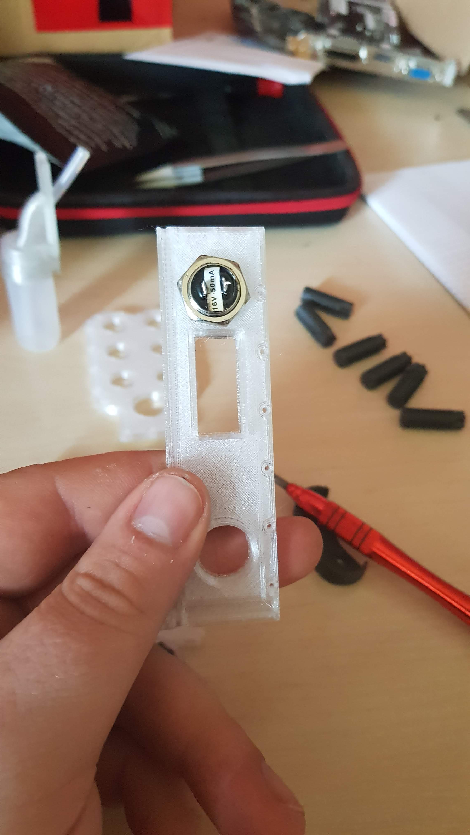
Ratte and Variations/doc/images/building/wisent/preparing_squonk_bottle17.png
