johannes-otto/Librecig/Ratte and Variations/doc/images/building/wisent/soldering_and_first_test_done (1).png

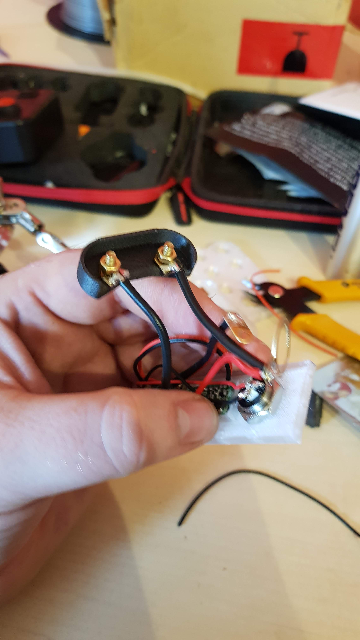
Ratte and Variations/doc/images/building/wisent/soldering_and_first_test_done (1).png
