johannes-otto/Librecig/Ratte and Variations/doc/images/building/wisent/top_contact_plate_inside_mod.png

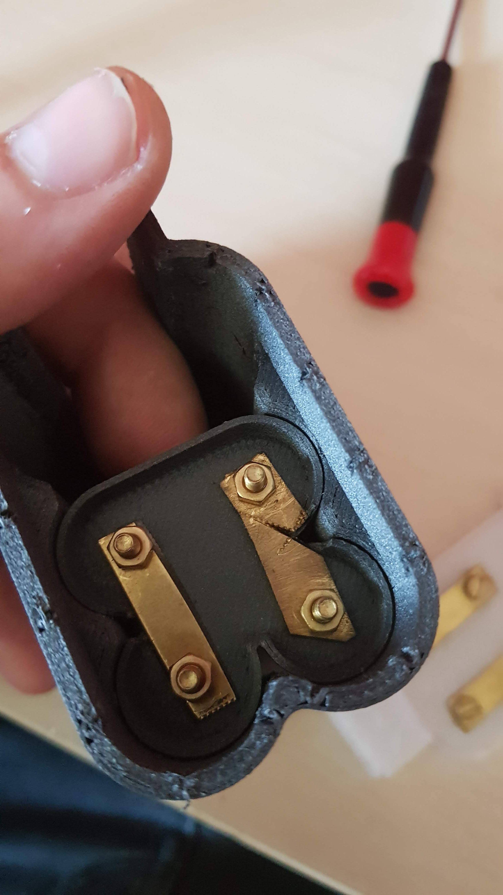
Ratte and Variations/doc/images/building/wisent/top_contact_plate_inside_mod.png
