johannes-otto/Librecig/Ratte and Variations/doc/images/wire diagrams/iPWM Wiring Diagram.jpg

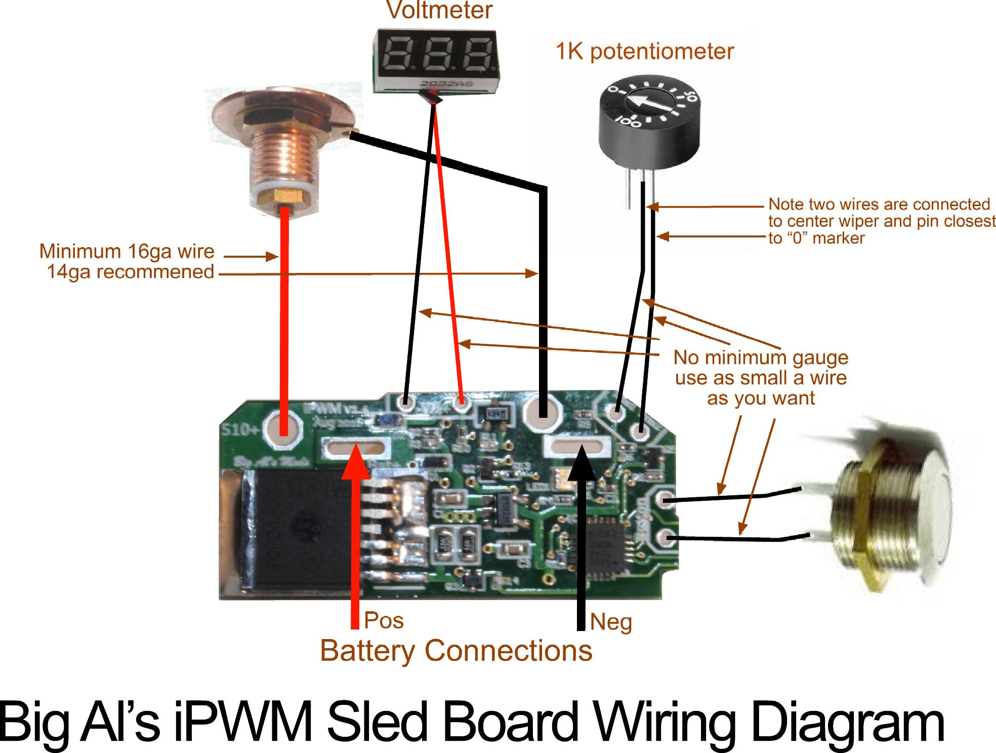
Ratte and Variations/doc/images/wire diagrams/iPWM Wiring Diagram.jpg
