johannes-otto/Librecig/Ratte and Variations/doc/images/building/wisent/final testing phase (2).png

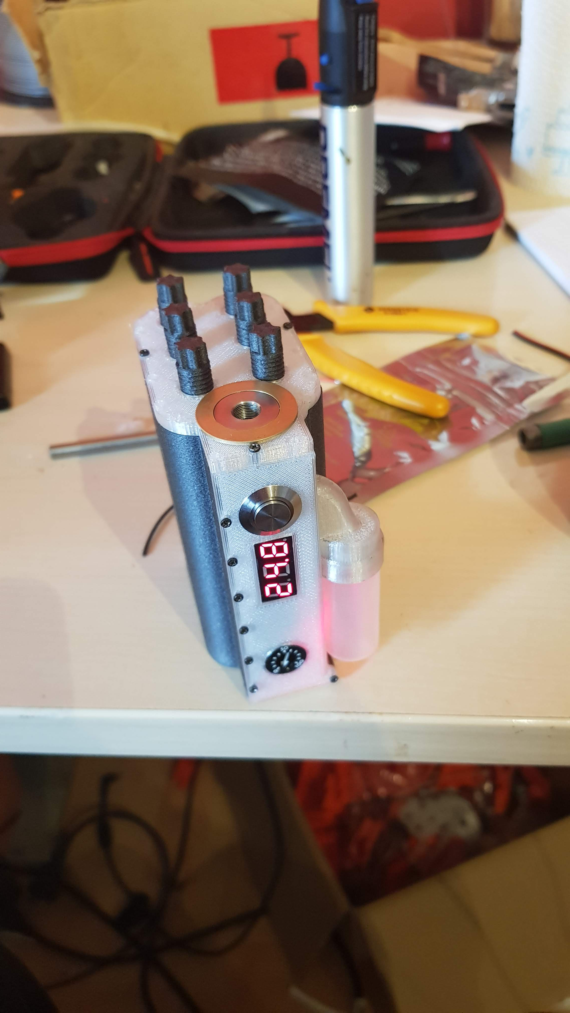
Ratte and Variations/doc/images/building/wisent/final testing phase (2).png
